hamddan4/rlpratbot/Code/TelegramBot/v2/RAT/GPS.h

/*H========================================================================
* FILENAME :        GPS.h
*
* DESCRIPTION :
*       All functions to retrieve data from GPS will be here. 
*       This file is a modification from the primary example of this GPS.
* 
* AUTHORS :    RLP Group 09-03
*                 - Daniel Azemar   dani.azemar@gmail.com
*                 - Jialuo Chen     
*                 - Sergi Pous
*                 - Adria Rico
*                 
* START DATE :    Apr 2017
* 
*========================================================================H*/

#include <Adafruit_GPS.h>
#include <SoftwareSerial.h>
SoftwareSerial mySerial(8, 7);

Adafruit_GPS GPS(&mySerial);

// Set GPSECHO to 'false' to turn off echoing the GPS data to the Serial console
// Set to 'true' if you want to debug and listen to the raw GPS sentences. 
#define GPSECHO  false

// this keeps track of whether we're using the interrupt
// off by default!
boolean usingInterrupt = false;
void useInterrupt(boolean); // Func prototype keeps Arduino 0023 happy

uint32_t timer = millis();

void setup_GPS()  
{
  // 9600 NMEA is the default baud rate for Adafruit MTK GPS's- some use 4800
  GPS.begin(9600);
  
  // uncomment this line to turn on RMC (recommended minimum) and GGA (fix data) including altitude
  GPS.sendCommand(PMTK_SET_NMEA_OUTPUT_RMCGGA);

  // Set the update rate
  GPS.sendCommand(PMTK_API_SET_FIX_CTL_1HZ  );   // 1 Hz update rate
  // For the parsing code to work nicely and have time to sort thru the data, and
  // print it out we don't suggest using anything higher than 1 Hz

  // Request updates on antenna status, comment out to keep quiet
  GPS.sendCommand(PGCMD_ANTENNA);

  // the nice thing about this code is you can have a timer0 interrupt go off
  // every 1 millisecond, and read data from the GPS for you. that makes the
  // loop code a heck of a lot easier!
  useInterrupt(true);

  delay(1000);
  // Ask for firmware version
  mySerial.println(PMTK_Q_RELEASE);
}

// Interrupt is called once a millisecond, looks for any new GPS data, and stores it
SIGNAL(TIMER0_COMPA_vect) {
  char c = GPS.read();
  // if you want to debug, this is a good time to do it!
  #ifdef UDR0
    if (GPSECHO)
      if (c) UDR0 = c;  
      // writing direct to UDR0 is much much faster than Serial.print 
      // but only one character can be written at a time. 
  #endif
}

void useInterrupt(boolean v) {
  if (v) {
    // Timer0 is already used for millis() - we'll just interrupt somewhere
    // in the middle and call the "Compare A" function above
    OCR0A = 0xAF;
    TIMSK0 |= _BV(OCIE0A);
    usingInterrupt = true;
  } else {
    // do not call the interrupt function COMPA anymore
    TIMSK0 &= ~_BV(OCIE0A);
    usingInterrupt = false;
  }
}

void GPS_loop()                     // run over and over again
{  
 // in case you are not using the interrupt above, you'll
  // need to 'hand query' the GPS, not suggested :(

  char c = GPS.read();
  if (! usingInterrupt) {
    // read data from the GPS in the 'main loop'
    char c = GPS.read();
    // if you want to debug, this is a good time to do it!
    if (GPSECHO)
      if (c) Serial.print(c);
  }
  
  // if a sentence is received, we can check the checksum, parse it...
  if (GPS.newNMEAreceived()) {
    // a tricky thing here is if we print the NMEA sentence, or data
    // we end up not listening and catching other sentences! 
    // so be very wary if using OUTPUT_ALLDATA and trytng to print out data
    //Serial.println(GPS.lastNMEA());   // this also sets the newNMEAreceived() flag to false
  
    if (!GPS.parse(GPS.lastNMEA()))   // this also sets the newNMEAreceived() flag to false
      return;  // we can fail to parse a sentence in which case we should just wait for another
  }

  // if millis() or timer wraps around, we'll just reset it
  if (timer > millis())  timer = millis();
}

boolean get_fix(){
  return (boolean)GPS.fix;
}

double get_latitude(){
  return GPS.latitudeDegrees;
}

double get_longitude(){
  return GPS.longitudeDegrees;
}
/*************************************************************************
 * //Function to calculate the distance between two waypoints
 *************************************************************************/
float calc_dist(float flat1, float flon1, float flat2, float flon2)
{
  float diflat = radians(flat2-flat1);
  flat1 = radians(flat1);
  flat2 = radians(flat2);
  float diflon = radians((flon2)-(flon1));

  //I've to spplit all the calculation in several steps. If i try to do it in a single line the arduino will explode.
  float dist_calc = (sin(diflat/2.0)*sin(diflat/2.0));
  float dist_calc2 = cos(flat1) * cos(flat2) *
                     sin(diflon/2.0) * sin(diflon/2.0);
                   
  dist_calc += dist_calc2;
  
  dist_calc=(2*atan2(sqrt(dist_calc),sqrt(1.0-dist_calc)));
  
  dist_calc*=6371000.0; //Converting to meters
  //Serial.println(dist_calc);
  return dist_calc;
}
