hamddan4/rlpratbot/Code/TelegramBot/v2/RAT/sonar.h

/*H========================================================================
* FILENAME :        sonar.h
*
* DESCRIPTION :
*       All function to retrieve data from sonar.
* 
* AUTHORS :    RLP Group 09-03
*                 - Daniel Azemar   dani.azemar@gmail.com
*                 - Jialuo Chen     
*                 - Sergi Pous
*                 - Adria Rico
*                 
* START DATE :    Feb 2017
* 
*========================================================================H*/

#define trigPin 3
#define echoPin 4


const double c = 20; // temperature in Cº
const double soundSpeed = 331.3 + (0.6 * c); // approximate speed of sound (in m/s) at temperature c

void setup_sonar(){
  pinMode(trigPin, OUTPUT); // pin to send waves
  pinMode(echoPin, INPUT); // pin to recieve echo waves
}

double getSonarDistance() {
  // resets the trig pin
  digitalWrite(trigPin, LOW);
  delayMicroseconds(2);
  // sets the trig pin to 1 for 100ms (must set for this long for the sonar to send waves)
  digitalWrite(trigPin, HIGH);
  delayMicroseconds(100);
  digitalWrite(trigPin, LOW);
  // reads the travel time (in micro seconds) of the echo wave from the echo pin

  unsigned long res_echo = pulseIn(echoPin, HIGH, 20000);
  
  float distance = (res_echo * soundSpeed) / 20000;
  return distance;
}
