hamddan4/rlpratbot/Code/Test/GPS/gps_shield-testing/gps_shield-testing.ino

#include <Adafruit_GPS.h>

// this sketch will allow you to bypass the Atmega chip
// and connect the GPS directly to the USB/Serial
// chip converter.
// Connect VIN to +5Vx
// Connect GND to Ground
// Connect GPS RX (data into GPS) to Digital 0
// Connect GPS TX (data out from GPS) to Digital 1

void setup() {}

void loop() {}
